tonyp7/esp32-nixie-clock/pcb/clock-face/esp32-nixie-clock-face-bottom-render.png

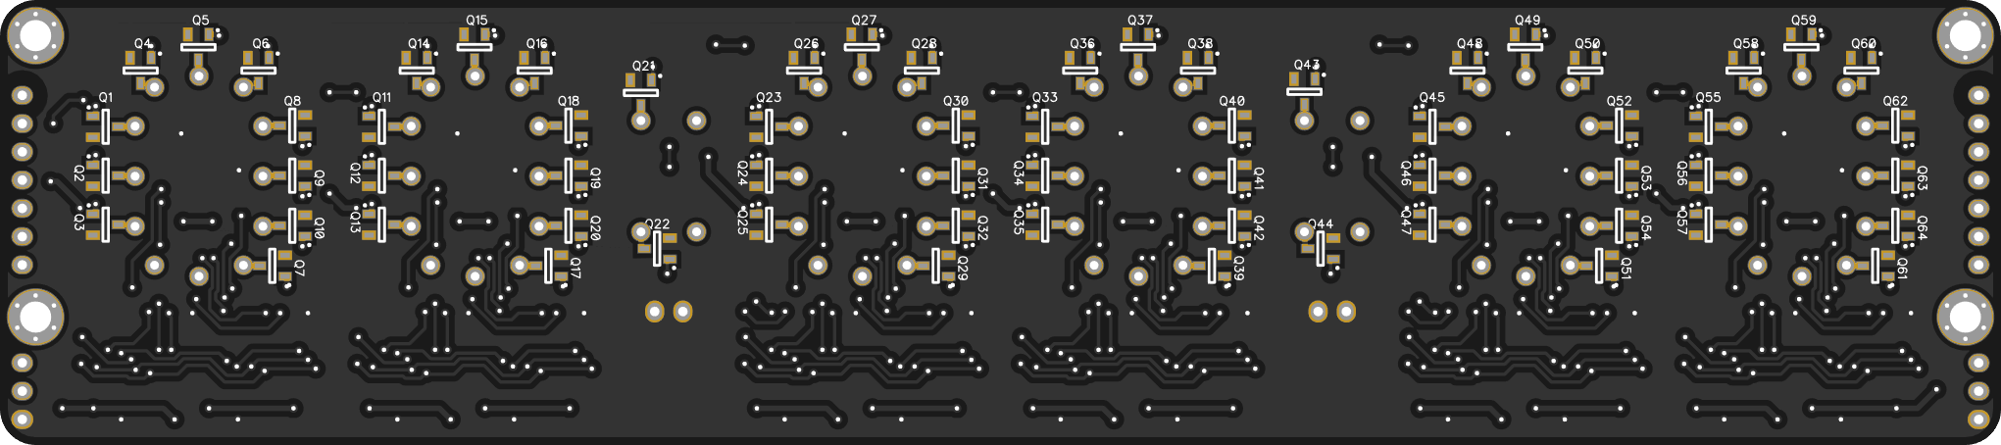
pcb/clock-face/esp32-nixie-clock-face-bottom-render.png
