tonyp7/esp32-nixie-clock/pcb/clock-face/esp32-nixie-clock-face-top-render.png

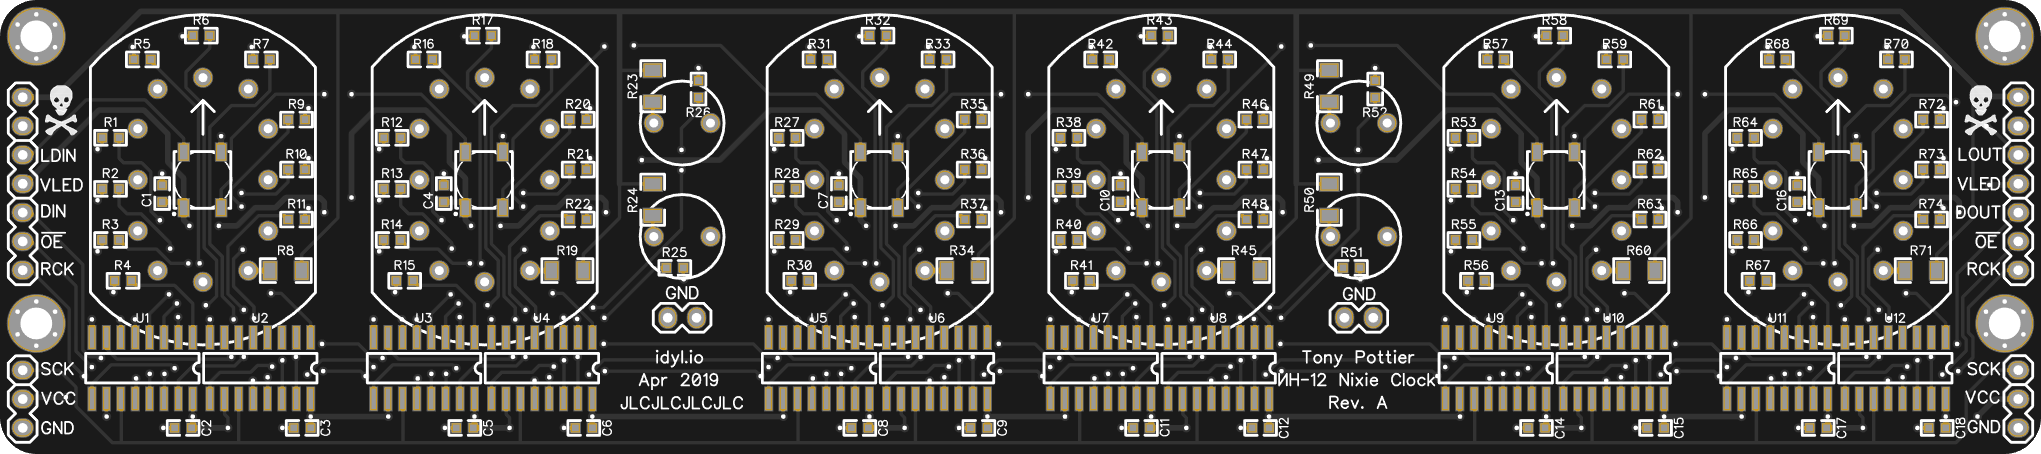
pcb/clock-face/esp32-nixie-clock-face-top-render.png
