tonyp7/esp32-nixie-clock/pcb/logic-board/esp32-nixie-clock-logic-board-bottom-render.png

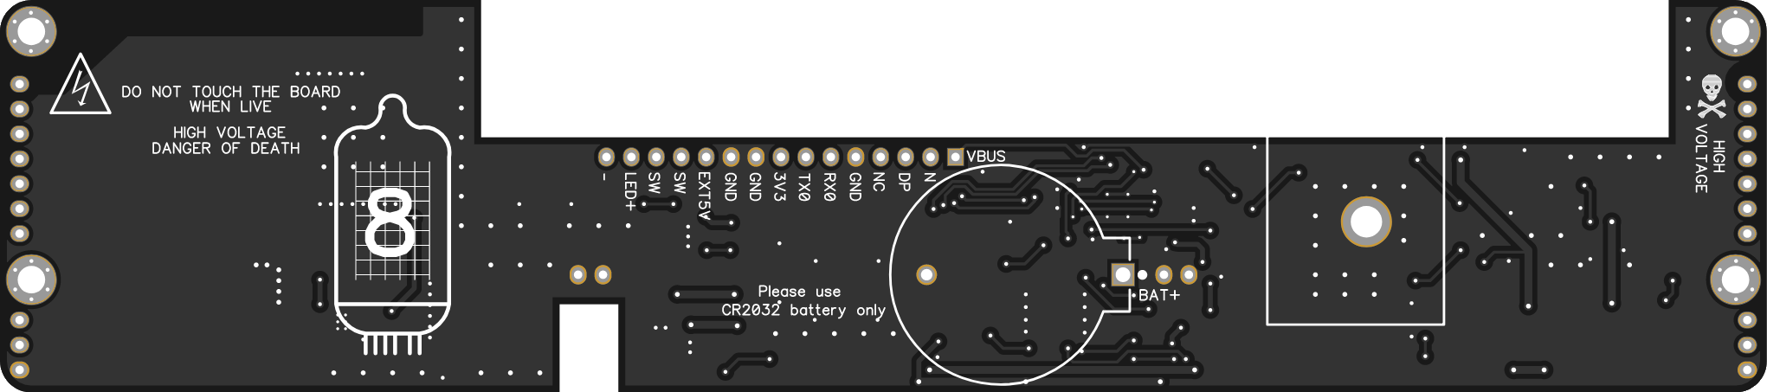
pcb/logic-board/esp32-nixie-clock-logic-board-bottom-render.png
