tonyp7/esp32-nixie-clock/pictures/face-clock-wip.jpg

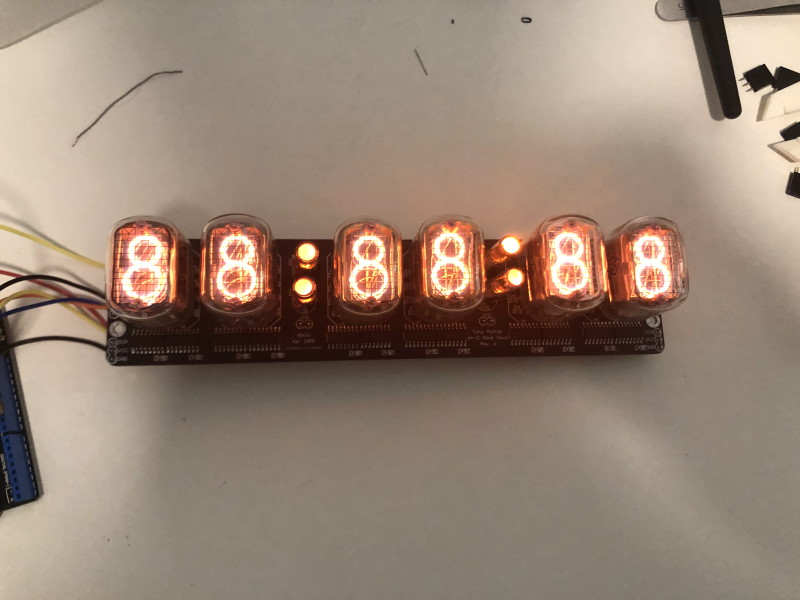
pictures/face-clock-wip.jpg
