tonyp7/esp32-nixie-clock/schematics/clock-face/clock-face-schematics-sheet-1.png

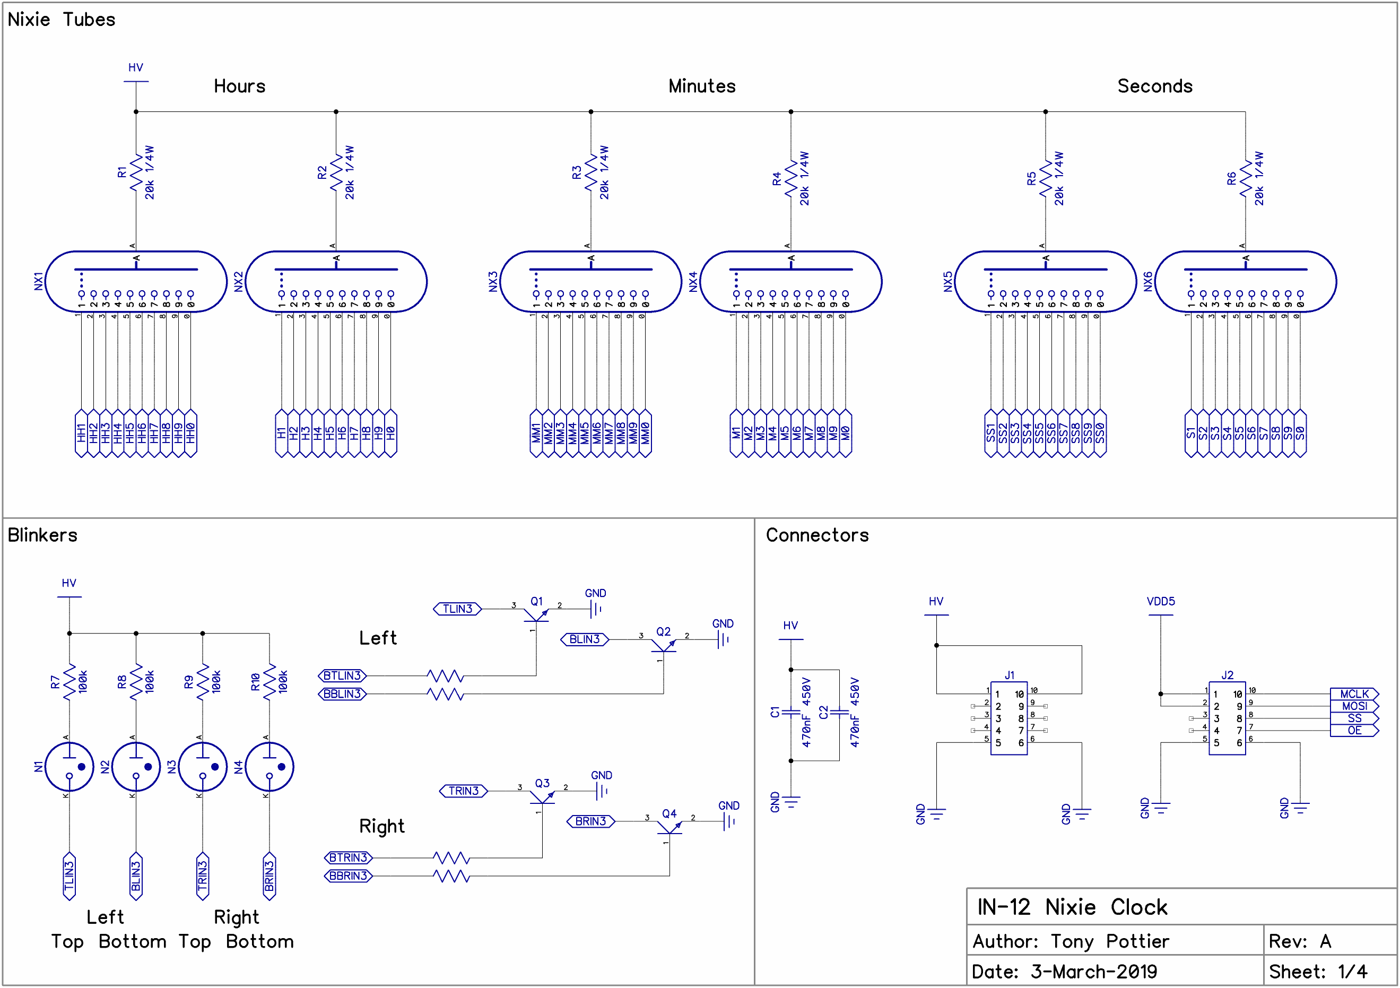
schematics/clock-face/clock-face-schematics-sheet-1.png
