tonyp7/esp32-nixie-clock/schematics/logic-board/logic-board-schematics-sheet-2.png

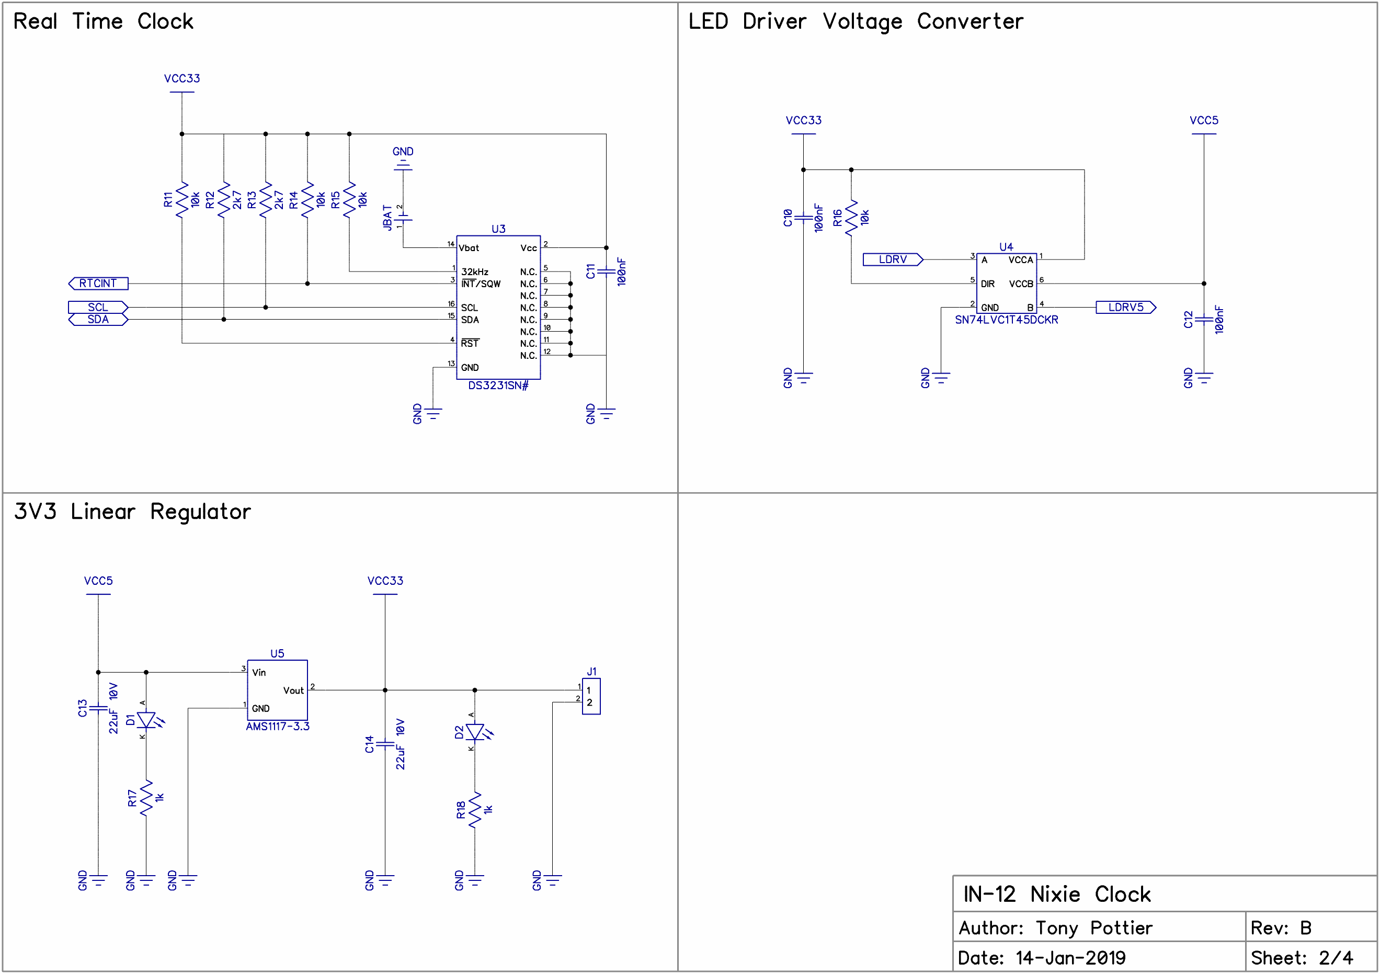
schematics/logic-board/logic-board-schematics-sheet-2.png
