tonyp7/esp32-nixie-clock/nixie_clock_code/main/webapp.c

/**
Copyright (c) 2020 Tony Pottier

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
@file webapp.c
@author Tony Pottier

Contains page logic handling web app functionalities

*/

#include <stdio.h>
#include <string.h>
#include <esp_log.h>
#include <esp_system.h>
#include <esp_http_server.h>
#include <sys/param.h> /* for the MIN macro */
#include <esp_err.h>
#include <cJSON.h>
#include <http_app.h>

#include "ws2812.h"
#include "display.h"
#include "clock.h"
#include "webapp.h"


/**
 * @brief embedded binary data.
 * @see file "CMakeLists.txt"
 * @see https://docs.espressif.com/projects/esp-idf/en/latest/api-guides/build-system.html#embedding-binary-data
 */
extern const uint8_t clock_css_start[] asm("_binary_clock_css_start");
extern const uint8_t clock_css_end[]   asm("_binary_clock_css_end");
extern const uint8_t clock_js_start[] asm("_binary_clock_js_start");
extern const uint8_t clock_js_end[] asm("_binary_clock_js_end");
extern const uint8_t clock_html_start[] asm("_binary_clock_html_start");
extern const uint8_t clock_html_end[] asm("_binary_clock_html_end");
extern const uint8_t iro_js_start[] asm("_binary_iro_js_start");
extern const uint8_t iro_js_end[] asm("_binary_iro_js_end");
extern const uint8_t timezones_json_start[] asm("_binary_timezones_json_start");
extern const uint8_t timezones_json_end[] asm("_binary_timezones_json_end");


/* const httpd related values stored in ROM */
const static char http_200_hdr[] = "200 OK";
const static char http_400_hdr[] = "400 Bad Request";
//const static char http_503_hdr[] = "503 Service Unavailable";
const static char http_content_type_html[] = "text/html";
const static char http_content_type_txt[] = "text/plain";
const static char http_content_type_js[] = "text/javascript";
const static char http_content_type_css[] = "text/css";
const static char http_content_type_json[] = "application/json";
const static char http_cache_control_hdr[] = "Cache-Control";
const static char http_cache_control_no_cache[] = "no-store, no-cache, must-revalidate, max-age=0";
const static char http_cache_control_cache[] = "public, max-age=31536000";
const static char http_pragma_hdr[] = "Pragma";
const static char http_pragma_no_cache[] = "no-cache";

const static char TAG[] = "webapp";





static cJSON* webapp_get_display_cjson(display_config_t *display){

    cJSON *root = cJSON_CreateObject();

    cJSON *rgb = cJSON_CreateObject();
    cJSON_AddNumberToObject( rgb, "r", display->led_color.r);
    cJSON_AddNumberToObject( rgb, "g", display->led_color.g);
    cJSON_AddNumberToObject( rgb, "b", display->led_color.b);
    cJSON_AddItemToObject(root, "led_color", rgb);

    return root;
}

static cJSON* webapp_get_timezone_cjson(timezone_t *timezone){

    /* format as following
        {
            "name": "Asia/Singapore"
        }
    */

   cJSON *root = cJSON_CreateObject();
   cJSON_AddStringToObject( root, "name", timezone->name );

   return root;
}

static cJSON* webapp_get_sleemodes_cjson(sleepmodes_t *sleepmodes){

	/* format as following:

	{
    "enabled":true,
    "data":[
        {"enabled":true,"days":3,"from":50400,"to":50460},
        {"enabled":false,"days":0,"from":0,"to":0},
        {"enabled":false,"days":0,"from":0,"to":0},
        {"enabled":false,"days":0,"from":0,"to":0}
	}
	*/

    cJSON *root = cJSON_CreateObject();
	cJSON *data = cJSON_CreateArray();

	cJSON_AddBoolToObject( root, "enabled", sleepmodes->enable_sleepmode );
	for(int i=0; i < CLOCK_MAX_SLEEPMODES; i++){

		cJSON *sleepmode = cJSON_CreateObject();
		cJSON_AddBoolToObject( sleepmode, "enabled", sleepmodes->sleepmode[i].enabled );
		cJSON_AddNumberToObject( sleepmode, "days", sleepmodes->sleepmode[i].days );
		cJSON_AddNumberToObject( sleepmode, "from", sleepmodes->sleepmode[i].from );
		cJSON_AddNumberToObject( sleepmode, "to", sleepmodes->sleepmode[i].to );

		cJSON_AddItemToArray( data, sleepmode);
	}
	cJSON_AddItemToObject(root, "data", data);

    return root;
}

static cJSON* webapp_get_config_cjson(clock_config_t *config){

    cJSON *root = cJSON_CreateObject();

    cJSON *timezone = webapp_get_timezone_cjson(  &((*config).timezone) );
    cJSON *sleepmodes = webapp_get_sleemodes_cjson(  &((*config).sleepmodes) );
    cJSON *display = webapp_get_display_cjson(  &((*config).display) );


    cJSON_AddItemToObject(root, "timezone", timezone);
    cJSON_AddItemToObject(root, "sleepmodes", sleepmodes);
    cJSON_AddItemToObject(root, "display", display);

    return root;
}

/**
 * @brief transforms a clock_config_t struct into its json string representation
 */
static char* webapp_get_config_json(clock_config_t config){

    cJSON *conf = webapp_get_config_cjson( &config );
    char* str_json = cJSON_Print(conf);
    cJSON_Delete(conf);

    return str_json;
}

/**
 * @brief transform a sleepmodes_t struct into its json string representation
 */
static char* webapp_get_sleepmodes_json(sleepmodes_t sleepmodes){

	char* str_json = NULL;

	/* format as following:

	{
    "enabled":true,
    "data":[
        {"enabled":true,"days":3,"from":50400,"to":50460},
        {"enabled":false,"days":0,"from":0,"to":0},
        {"enabled":false,"days":0,"from":0,"to":0},
        {"enabled":false,"days":0,"from":0,"to":0}
	}
	*/

	cJSON *root = cJSON_CreateObject();
	cJSON *data = cJSON_CreateArray();

	cJSON_AddBoolToObject( root, "enabled", sleepmodes.enable_sleepmode );
	for(int i=0; i < CLOCK_MAX_SLEEPMODES; i++){

		cJSON *sleepmode = cJSON_CreateObject();
		cJSON_AddBoolToObject( sleepmode, "enabled", sleepmodes.sleepmode[i].enabled );
		cJSON_AddNumberToObject( sleepmode, "days", sleepmodes.sleepmode[i].days );
		cJSON_AddNumberToObject( sleepmode, "from", sleepmodes.sleepmode[i].from );
		cJSON_AddNumberToObject( sleepmode, "to", sleepmodes.sleepmode[i].to );

		cJSON_AddItemToArray( data, sleepmode);
	}
	cJSON_AddItemToObject(root, "data", data);

	str_json = cJSON_Print(root);
	cJSON_Delete(root);

	return str_json;
}

static esp_err_t webapp_get_hander(httpd_req_t *req){

    if(strcmp(req->uri, "/") == 0){

        httpd_resp_set_status(req, http_200_hdr);
		httpd_resp_set_type(req, http_content_type_html);
		httpd_resp_send(req, (char*)clock_html_start, clock_html_end - clock_html_start);
    }
    else if(strcmp(req->uri, "/clock.js") == 0){

        httpd_resp_set_status(req, http_200_hdr);
		httpd_resp_set_type(req, http_content_type_js);
        httpd_resp_set_hdr(req, http_cache_control_hdr, http_cache_control_cache);
		httpd_resp_send(req, (char*)clock_js_start, clock_js_end - clock_js_start);
    }
    else if(strcmp(req->uri, "/iro.min.js") == 0){

        httpd_resp_set_status(req, http_200_hdr);
		httpd_resp_set_type(req, http_content_type_js);
        httpd_resp_set_hdr(req, http_cache_control_hdr, http_cache_control_cache);
		httpd_resp_send(req, (char*)iro_js_start, iro_js_end - iro_js_start);
    }
    else if(strcmp(req->uri, "/clock.css") == 0){

        httpd_resp_set_status(req, http_200_hdr);
		httpd_resp_set_type(req, http_content_type_css);
        httpd_resp_set_hdr(req, http_cache_control_hdr, http_cache_control_cache);
		httpd_resp_send(req, (char*)clock_css_start, clock_css_end - clock_css_start);
    }
    else if(strcmp(req->uri, "/timezones.json") == 0){

        httpd_resp_set_status(req, http_200_hdr);
		httpd_resp_set_type(req, http_content_type_json);
		httpd_resp_send(req, (char*)timezones_json_start, timezones_json_end - timezones_json_start);
    }
    else if(strcmp(req->uri, "/timezone/") == 0){

        clock_config_t conf = clock_get_config();

        httpd_resp_set_status(req, http_200_hdr);
		httpd_resp_set_type(req, http_content_type_txt);
        httpd_resp_set_hdr(req, http_cache_control_hdr, http_cache_control_no_cache);
        httpd_resp_set_hdr(req, http_pragma_hdr, http_pragma_no_cache);
        httpd_resp_send(req, conf.timezone.name, strlen( conf.timezone.name ));
        
    }
    else if(strcmp(req->uri, "/config/") == 0){

        char* str_json = webapp_get_config_json( clock_get_config() );

        if(str_json){

            httpd_resp_set_status(req, http_200_hdr);
            httpd_resp_set_type(req, http_content_type_json);
            httpd_resp_set_hdr(req, http_cache_control_hdr, http_cache_control_no_cache);
            httpd_resp_set_hdr(req, http_pragma_hdr, http_pragma_no_cache);
            httpd_resp_send(req, str_json, strlen(str_json));

            free(str_json);

            return ESP_OK;
        }
        else{
            httpd_resp_send_500(req);
            return ESP_FAIL;
        }

    }
    else if(strcmp(req->uri, "/sleepmode/") == 0){

        clock_config_t conf = clock_get_config();
        char* str_json = webapp_get_sleepmodes_json( conf.sleepmodes );

        if(str_json){

            httpd_resp_set_status(req, http_200_hdr);
            httpd_resp_set_type(req, http_content_type_json);
            httpd_resp_set_hdr(req, http_cache_control_hdr, http_cache_control_no_cache);
            httpd_resp_set_hdr(req, http_pragma_hdr, http_pragma_no_cache);
            httpd_resp_send(req, str_json, strlen(str_json));

            free(str_json);

            return ESP_OK;
        }
        else{
            httpd_resp_send_500(req);
            return ESP_FAIL;
        }
    }
    else{

        httpd_resp_send_404(req);
    }

    return ESP_OK;
}

/**
 * @brief Parses a json string into a sleepmodes_t struct 
 */
static esp_err_t webapp_parse_sleemodes(char *content, sleepmodes_t *sleepmodes){

    sleepmodes_t sm;
    memset(&sm, 0x00, sizeof(sleepmodes_t));
    
    cJSON *json = cJSON_Parse(content);
    if(json == NULL){

        const char *error_ptr = cJSON_GetErrorPtr();
        ESP_LOGE(TAG, "cJSON parsing error: %s", error_ptr);
        return ESP_FAIL;
    }

    cJSON *enable_sleepmode = cJSON_GetObjectItemCaseSensitive(json, "enabled");
    sm.enable_sleepmode = (bool)enable_sleepmode->valueint;

    cJSON *data = cJSON_GetObjectItemCaseSensitive(json, "data");
    cJSON *sleepmode;
    int i = 0;

    cJSON_ArrayForEach(sleepmode, data){
        cJSON *enabled = cJSON_GetObjectItemCaseSensitive(sleepmode, "enabled");
        cJSON *days = cJSON_GetObjectItemCaseSensitive(sleepmode, "days");
        cJSON *from = cJSON_GetObjectItemCaseSensitive(sleepmode, "from");
        cJSON *to = cJSON_GetObjectItemCaseSensitive(sleepmode, "to");

        sm.sleepmode[i].enabled = (bool)enabled->valueint;
        sm.sleepmode[i].days = days->valueint;
        sm.sleepmode[i].from = from->valueint;
        sm.sleepmode[i].to = to->valueint;
        i++;
        if(i >= CLOCK_MAX_SLEEPMODES) break;
    }

    cJSON_Delete(json);
    *sleepmodes = sm;

    return ESP_OK;
}

static esp_err_t webapp_post_handler(httpd_req_t *req){

    if(strcmp(req->uri, "/timezone/") == 0){
        /* process a timezone change. Expected content is in the format: 
            { "timezone" : "America\/Indiana\/Indianapolis" }
        */
        clock_config_t conf = clock_get_config();
        const size_t buffer_size = 60; 
        char content[buffer_size]; /* 60 byte is OK to just put on the stack */
        esp_err_t ret = ESP_OK;
        memset(content, 0x00, buffer_size);

        /* Truncate if content length larger than the buffer. If we fall on this case it means the request is probably buggy */
        size_t recv_size = MIN(req->content_len, sizeof(content));

        int read_count = httpd_req_recv(req, content, recv_size);
        if (read_count <= 0) {  /* 0 return value indicates connection closed */
            /* Check if timeout occurred */
            if (read_count == HTTPD_SOCK_ERR_TIMEOUT) {
                /* In case of timeout one can choose to retry calling
                    * httpd_req_recv(), but to keep it simple, here we
                    * respond with an HTTP 408 (Request Timeout) error */
                httpd_resp_send_408(req);
            }
            else {
                httpd_resp_send_500(req);
            }
            return ESP_FAIL;
        }

        /* avoids a buffer overflow parsing the string if the content is just the size of the buffer */
        content[buffer_size - 1] = '\0';

        /* parse to json */
        cJSON *json = cJSON_Parse(content);

        if(json == NULL){
            const char *error_ptr = cJSON_GetErrorPtr();
            ESP_LOGE(TAG, "cJSON parsing error: %s", error_ptr);

            /* bad request */
            httpd_resp_set_status(req, http_400_hdr);
            httpd_resp_send(req, NULL, 0);
            return ESP_FAIL;
        }

        cJSON *timezone = cJSON_GetObjectItemCaseSensitive(json, "timezone");

        if(strcmp(timezone->valuestring, conf.timezone.name) != 0){
            /* timezone change!*/
            clock_notify_new_timezone(timezone->valuestring);
        }

        cJSON_Delete(json);
        return ret;

    }
    else if(strcmp(req->uri, "/sleepmode/") == 0){


        const size_t max_buffer_size = 511;
        sleepmodes_t sleepmodes;
        esp_err_t ret = ESP_OK;
        
        /** read body buffer. The message should be in this format:
            {
                "enabled":	false,
                "data":	[{
                        "enabled":	false,
                        "days":	255,
                        "from":	99999,
                        "to":	99999
                    }, {
                        "enabled":	false,
                        "days":	255,
                        "from":	99999,
                        "to":	99999
                    }, {
                        "enabled":	false,
                        "days":	255,
                        "from":	99999,
                        "to":	99999
                    }, {
                        "enabled":	false,
                        "days":	255,
                        "from":	99999,
                        "to":	99999
                    }]
            }
         * that is to say never more than 400 chars.
         * because this is pretty big to be on the stack
         * it is heap allocated
         */

        /* Truncate if content length larger than the buffer */
        size_t recv_size = MIN(req->content_len, max_buffer_size);
        char* content = malloc(sizeof(char) * (recv_size+1));
        memset(content, 0x00, (recv_size+1));


        int read_count = httpd_req_recv(req, content, recv_size);
        if (read_count <= 0) {  /* 0 return value indicates connection closed */
            /* Check if timeout occurred */
            if (read_count == HTTPD_SOCK_ERR_TIMEOUT) {
                /* In case of timeout one can choose to retry calling
                    * httpd_req_recv(), but to keep it simple, here we
                    * respond with an HTTP 408 (Request Timeout) error */
                httpd_resp_send_408(req);
            }
            else {
                httpd_resp_send_500(req);
            }

            free(content);
            return ESP_FAIL;
        }

        
        /* processing -- build the sleepomodes_t object */
        ret = webapp_parse_sleemodes(content, &sleepmodes);
        if(ret == ESP_OK){

            /* send sleepmode over to the clock */
            clock_notify_new_sleepmodes(sleepmodes);

            /* web answer */
            httpd_resp_set_status(req, http_200_hdr);
            httpd_resp_set_type(req, http_content_type_json);
            httpd_resp_set_hdr(req, http_cache_control_hdr, http_cache_control_no_cache);
            httpd_resp_set_hdr(req, http_pragma_hdr, http_pragma_no_cache);
            httpd_resp_send(req, content, strlen(content));
            free(content);
            return ESP_OK;
        }
        else{
            httpd_resp_send_408(req);
            free(content);
            return ret;
        }

    }
    else if(strcmp(req->uri, "/backlights/") == 0){

        /* read body buffer. The message should be { r: 123, g: 123, b: 123 } that is to say never more than 30 chars. */
        const size_t buffer_size = 30;
        char content[buffer_size];
        esp_err_t ret = ESP_OK;
        memset(content, 0x00, buffer_size);

        /* Truncate if content length larger than the buffer */
        size_t recv_size = MIN(req->content_len, sizeof(content));

        int read_count = httpd_req_recv(req, content, recv_size);
        if (read_count <= 0) {  /* 0 return value indicates connection closed */
            /* Check if timeout occurred */
            if (read_count == HTTPD_SOCK_ERR_TIMEOUT) {
                /* In case of timeout one can choose to retry calling
                    * httpd_req_recv(), but to keep it simple, here we
                    * respond with an HTTP 408 (Request Timeout) error */
                httpd_resp_send_408(req);
            }
            else {
                httpd_resp_send_500(req);
            }
            return ESP_FAIL;
        }


        /* avoids a buffer overflow parsing the string if the content is bigger than the buffer size */
        content[buffer_size - 1] = '\0';

        /* parse content to json */
        rgb_t rgb = {.num = (uint32_t)0};
        cJSON *json = cJSON_Parse(content);
        const cJSON *r = NULL;
        const cJSON *g = NULL;
        const cJSON *b = NULL;

        if(json == NULL){

            const char *error_ptr = cJSON_GetErrorPtr();
            ESP_LOGE(TAG, "cJSON parsing error: %s", error_ptr);

            /* bad request */
            httpd_resp_set_status(req, http_400_hdr);
            httpd_resp_send(req, NULL, 0);
            return ESP_FAIL;

        }

        r = cJSON_GetObjectItemCaseSensitive(json, "r");
        g = cJSON_GetObjectItemCaseSensitive(json, "g");
        b = cJSON_GetObjectItemCaseSensitive(json, "b");

        if(r != NULL && g != NULL && b != NULL && cJSON_IsNumber(r) && cJSON_IsNumber(g) && cJSON_IsNumber(b)){

            rgb.r = (uint8_t)r->valueint;
            rgb.g = (uint8_t)g->valueint;
            rgb.b = (uint8_t)b->valueint;

            /* free json object */
            cJSON_Delete(json);

            ret = ws2812_set_backlight_color(rgb);
            clock_notify_new_backlight_color(rgb);
            if(ret == ESP_OK){

                httpd_resp_set_status(req, http_200_hdr);
                httpd_resp_send(req, NULL, 0);
                return ESP_OK;
            }
            else{
                httpd_resp_send_500(req);
                return ESP_FAIL;
            }
        }
        else{

            /* free json object */
            cJSON_Delete(json);

            /* bad request */
            httpd_resp_set_status(req, http_400_hdr);
            httpd_resp_send(req, NULL, 0);
            return ESP_FAIL;
        }

    } /* if(strcmp(req->uri, "/backlights/") == 0) */

    return ESP_OK;
}

esp_err_t webapp_register_handlers(){

    esp_err_t ret;
    ret = http_app_set_handler_hook(HTTP_GET, &webapp_get_hander);

    if(ret != ESP_OK){
        return ret;
    }

    ret = http_app_set_handler_hook(HTTP_POST, &webapp_post_handler);
    if(ret != ESP_OK){
        http_app_set_handler_hook(HTTP_POST, NULL);
        return ret;
    }

    return ESP_OK;
}
