tonyp7/esp32-nixie-clock/nixie_clock_code/main/list.c

/**
Copyright (c) 2020 Tony Pottier

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
@file list.c
@author Tony Pottier
@brief Simple C linked list

@see https://idyl.io
@see https://github.com/tonyp7/esp32-nixie-clock

*/

#include <stdlib.h>
#include "list.h"

list_t* list_create()
{

	list_t* list = malloc(sizeof(list_t));

	list->first = NULL;
	list->last = NULL;
	list->count = 0;

	return list;
}


void list_free(list_t* list) 
{

	node_t* next;
	node_t* curr = list->first;

	while (curr != NULL) {
		next = curr->next;
		free(curr);
		curr = next;
	}

	free(list);
}

void list_clear(list_t* list)
{
    node_t* next;
	node_t* curr = list->first;

	while (curr != NULL) {
		next = curr->next;
		free(curr);
		curr = next;
	}

    list->count = 0;
    list->first = NULL;
    list->last = NULL;
}



void list_push(list_t* list, LIST_DATA_TYPE data) 
{
	node_t* node = malloc(sizeof(node_t));
	node->data = data;
	node->next = NULL; /* sent to the end so there is no next */

	if ( list->last != NULL) {
		node_t* last = list->last;
		last->next = node;
		list->last = node;
	}
	else {

		list->first = node;
		list->last = node;
	}

	list->count++;
}



void list_add_ordered(list_t* list, LIST_DATA_TYPE data, int (*comp)(LIST_DATA_TYPE*, LIST_DATA_TYPE*))
{

	if (list->count == 0) return list_push(list, data);

	node_t* current = list->first;
	node_t* previous = NULL;

	/* create the node to add to the list */
	node_t* node = malloc(sizeof(node_t));
	node->data = data;
	

	/* find spot in list to add the new element */
	while (current != NULL && comp( &(current->data), &data) < 0) {
		previous = current;
		current = current->next;
	}
	node->next = current;

	if (previous == NULL) {
		/* added at the beginning of the list */
		list->first = node;

		/* in case this was the first element to be added */
		if (list->last == NULL) {
			list->last = node;
		}
	}
	else {

		/* the end of the list is the newly inserted node ? */
		if (list->last == previous) {
			list->last = node;
		}
		previous->next = node;
	}


	list->count++;

}


int list_shift(list_t* list, LIST_DATA_TYPE * data) 
{
	if (list->first) {
		node_t* first = list->first;
		LIST_DATA_TYPE shift_data = first->data;
		
		if (list->last == list->first) { /*edge case where list contains one element */
			list->first = NULL;
			list->last = NULL;
		}
		else {
			list->first = first->next;
		}

		free(first);
		list->count--;

		/* NULL can be passed as data. In that case value isn't sent back to caller */
		if(data){
			*data = shift_data;
		}
        
        return 0;
	}
	else {
		return -1;
	}
}


int list_peek(list_t* list, LIST_DATA_TYPE * data)
{
    if (list->first) {
        *data = list->first->data;
        return 0;
    }
    else{
        return -1;
    }
}

int list_pop(list_t* list, LIST_DATA_TYPE * data)
{
	if (list->last) {

		node_t* last = list->last;
		LIST_DATA_TYPE pop_data = last->data;

		if (list->last == list->first) { /*edge case where list contains one element */
			list->first = NULL;
			list->last = NULL;
		}
		else {
			node_t* current = list->first;
			while (current != NULL && current->next != list->last) {
				current = current->next;
			}
			current->next = NULL;
			list->last = current;
		}

		free(last);
		list->count--;

        *data = pop_data;
        return 0;

	}
	else {
		return -1;
	}
}
